BeyondMicroControl/EurorackSoundbar/illustrations/6N137_optocoupler.png

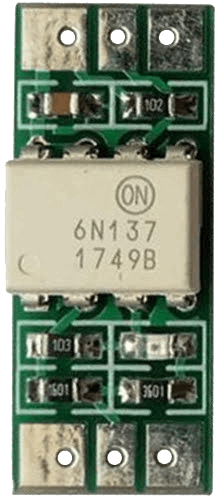
illustrations/6N137_optocoupler.png
