BeyondMicroControl/EurorackSoundbar/illustrations/amplifier2.jpg

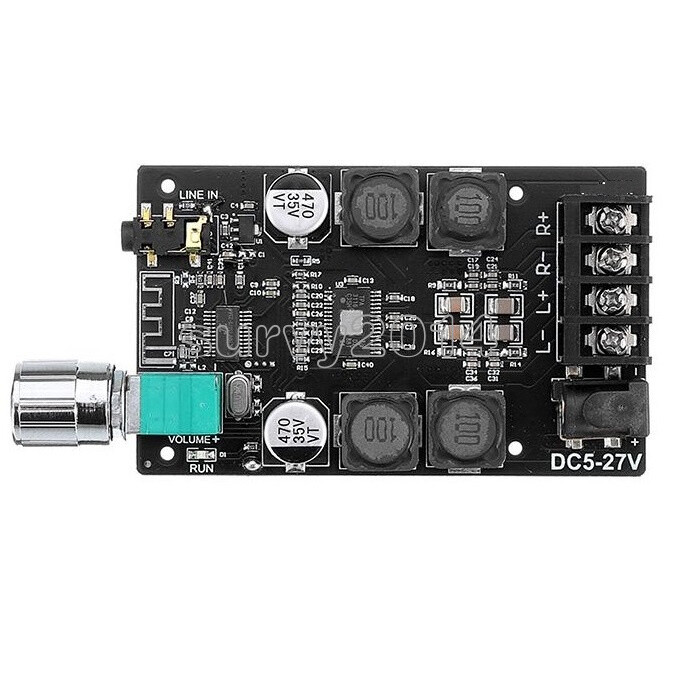
illustrations/amplifier2.jpg
