BeyondMicroControl/EurorackSoundbar/illustrations/amplifier.png

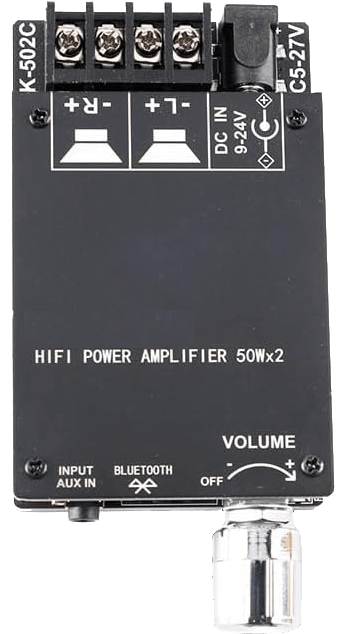
illustrations/amplifier.png
