BeyondMicroControl/EurorackSoundbar/illustrations/Chordio_Scales_01.png

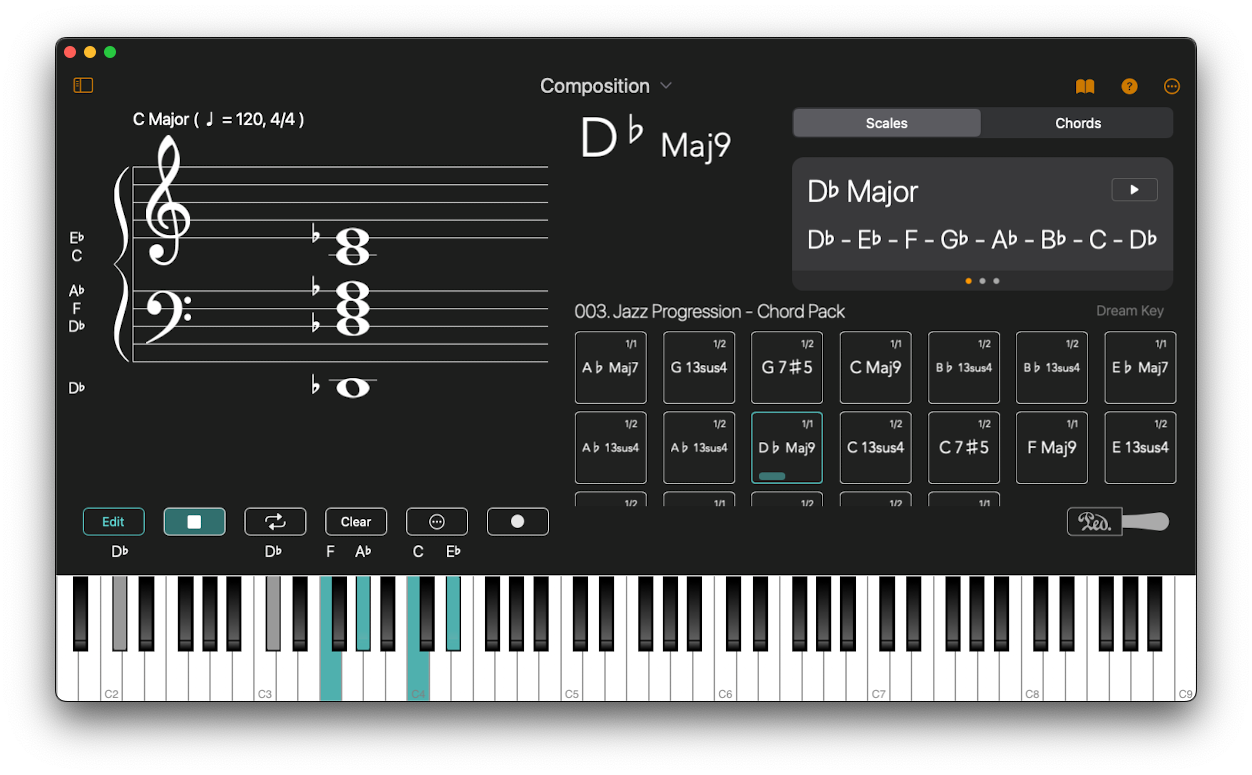
illustrations/Chordio_Scales_01.png
