BeyondMicroControl/EurorackSoundbar/illustrations/multicast.jpg

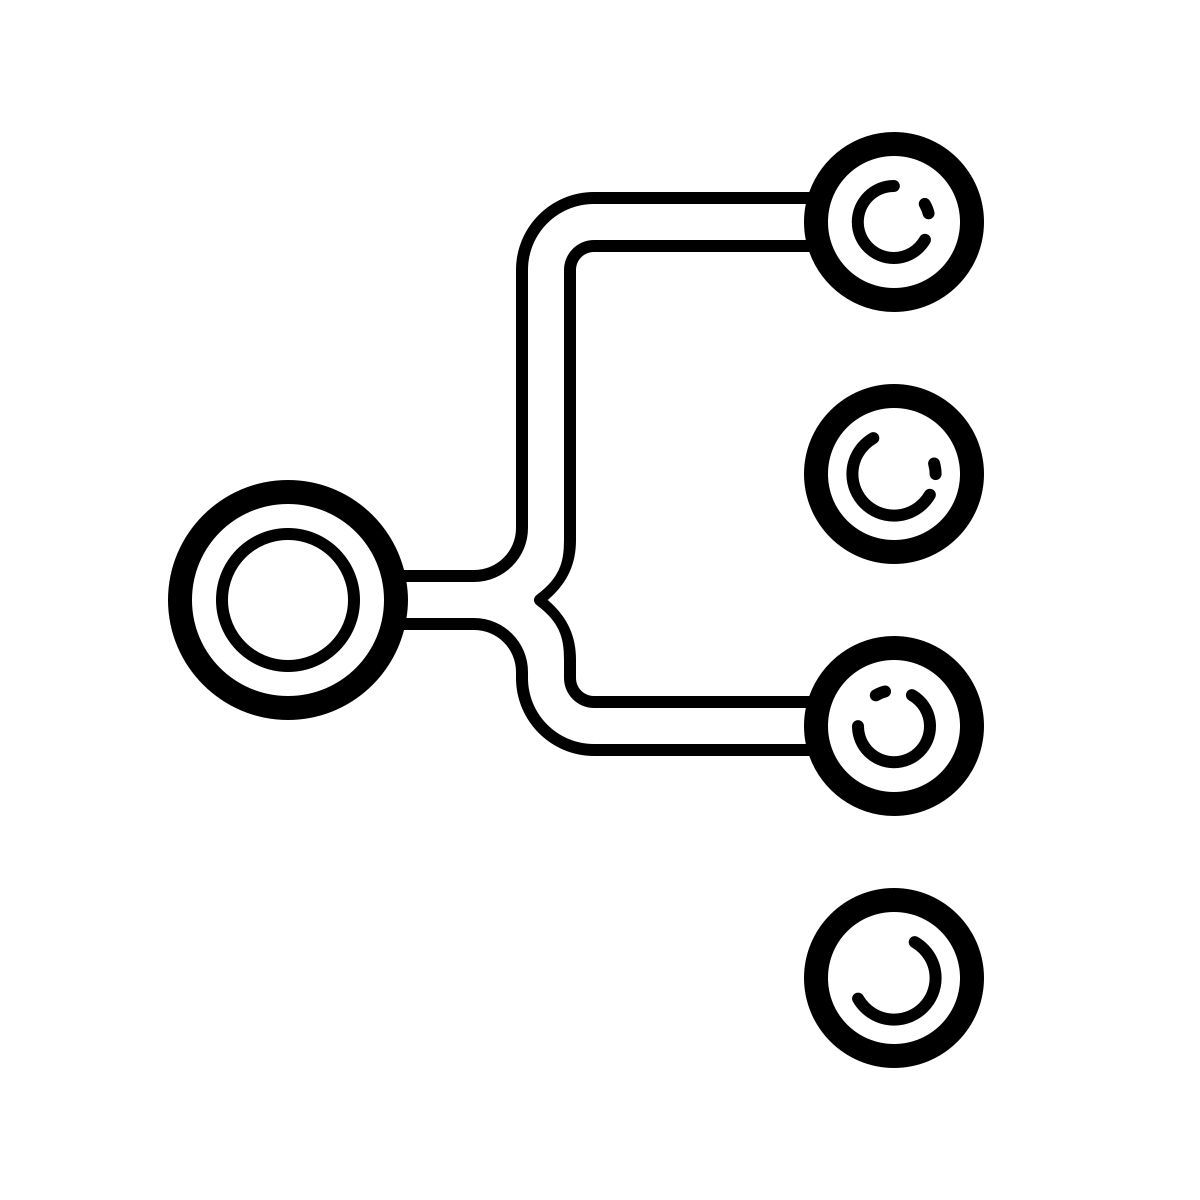
illustrations/multicast.jpg
