BeyondMicroControl/EurorackSoundbar/illustrations/Screenshot 2026-01-02 at 20.37.27.png

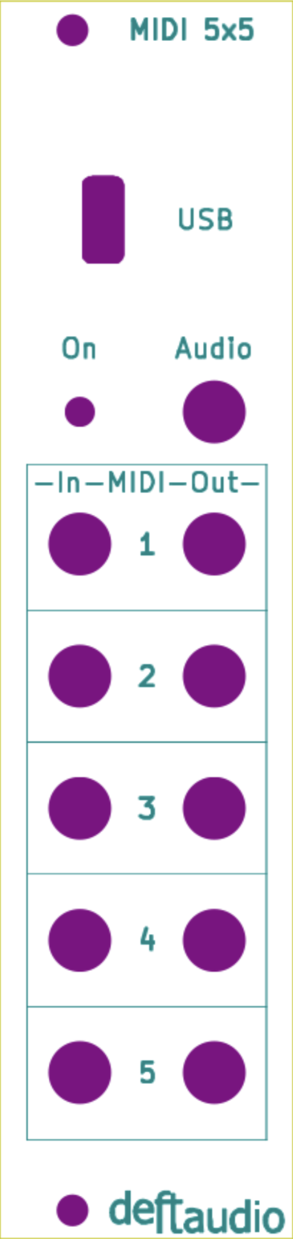
illustrations/Screenshot 2026-01-02 at 20.37.27.png
