BeyondMicroControl/EurorackSoundbar/illustrations/vpc1backpanel.jpng.png

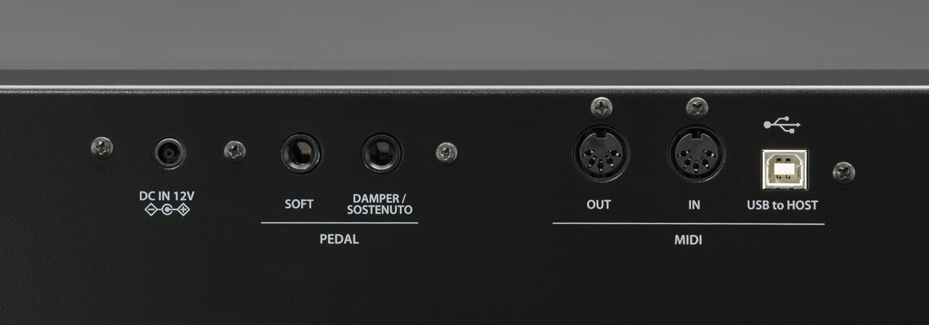
illustrations/vpc1backpanel.jpng.png
