BeyondMicroControl/EurorackSoundbar/res/envelope_200x200.png

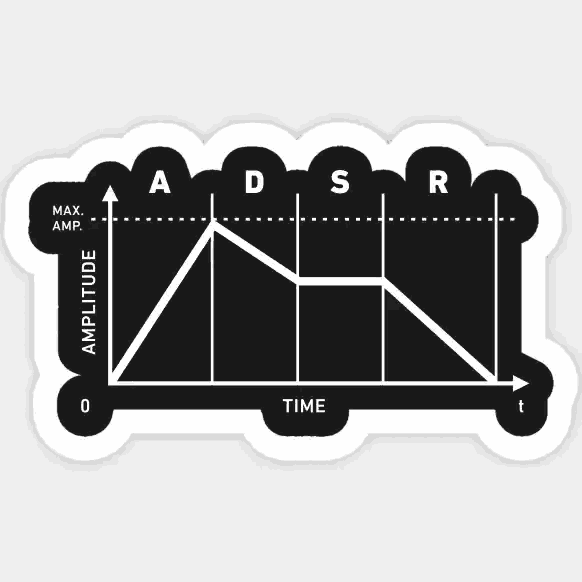
res/envelope_200x200.png
