BeyondMicroControl/EurorackSoundbar/res/SSD1306_200x200.png

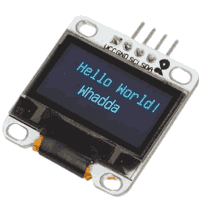
res/SSD1306_200x200.png
