BeyondMicroControl/EurorackSoundbar/schemas/Analog_5V.png

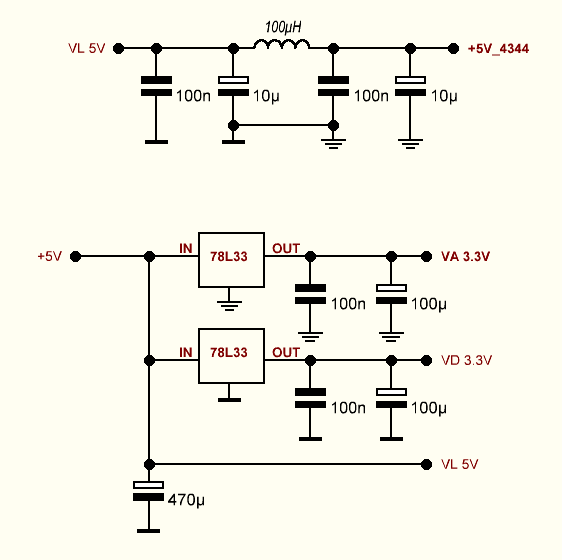
schemas/Analog_5V.png
