BeyondMicroControl/EurorackSoundbar/schemas/Screenshot 2025-11-29 at 17.39.31.png

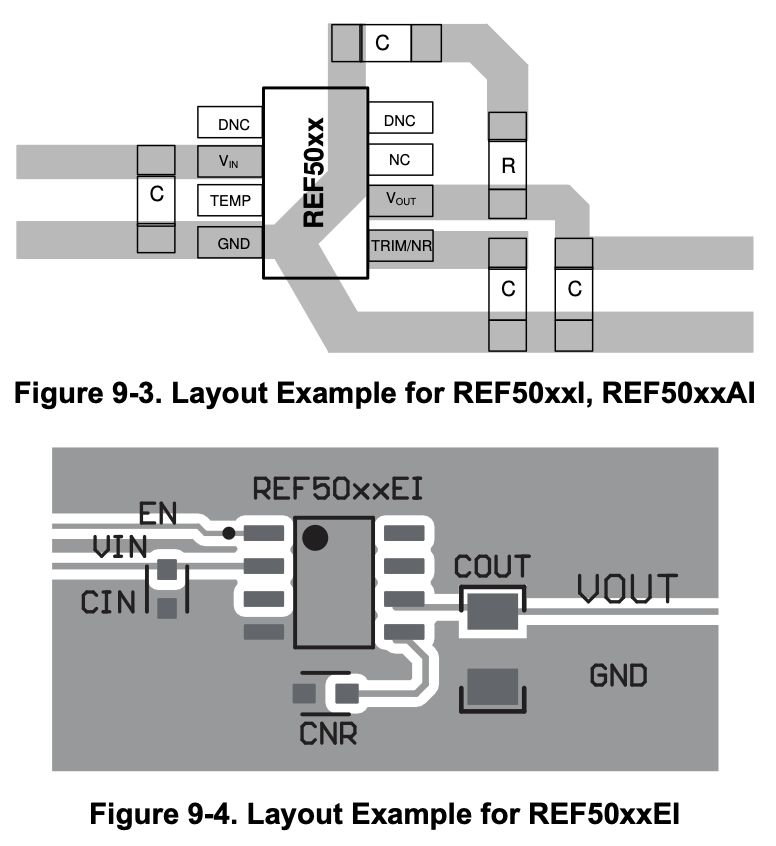
schemas/Screenshot 2025-11-29 at 17.39.31.png
